usbalex/74series_game_of_life/74series_game_of_life.kicad_sch

## KiCad design 74series_game_of_life.kicad_sch (2022-06-20)

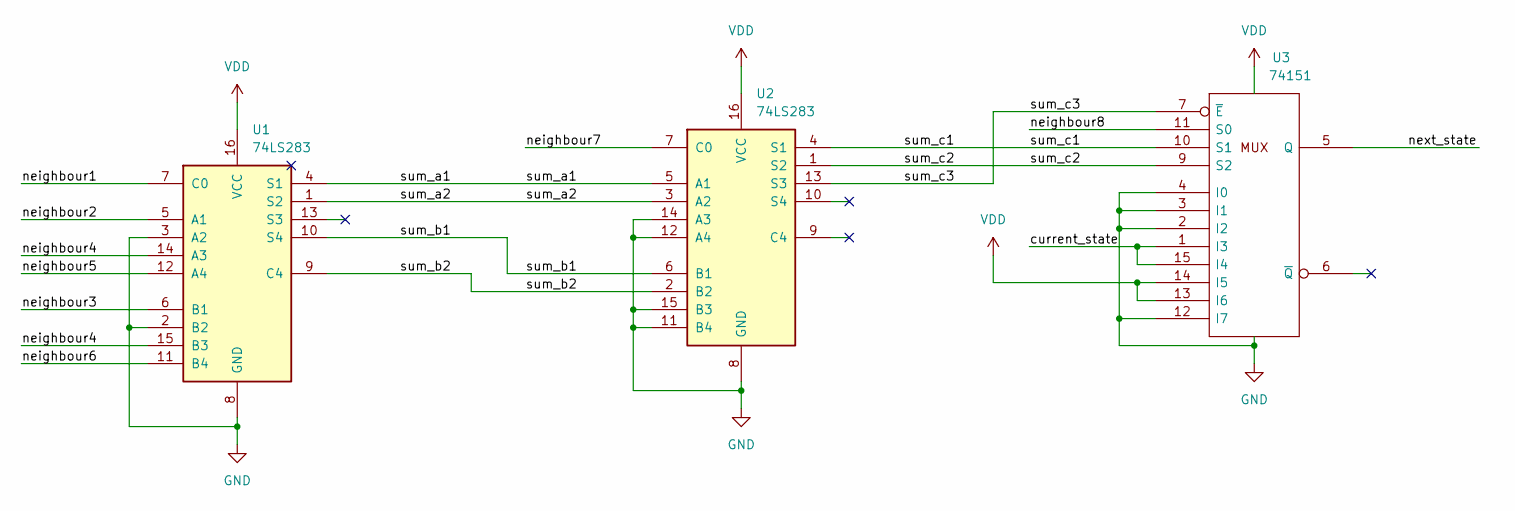
[picture p2: schematic 74series_game_of_life.kicad_sch]

Parts:
U1, U2: 74LS283
U3: 74151

Connections:
unnamed: U1.2 (B2), U1.3 (A2), U1.8 (GND)
unnamed: U2.8 (GND), U2.11 (B4), U2.12 (A4), U2.14 (A3), U2.15 (B3)
unnamed: U3.2 (I2), U3.3 (I1), U3.4 (I0), U3.8 (GND), U3.12 (I7)
unnamed: U3.13 (I6), U3.14 (I5)
current_state: U3.1 (I3), U3.15 (I4)
neighbour1: U1.7 (C0)
neighbour2: U1.5 (A1)
neighbour3: U1.6 (B1)
neighbour4: U1.14 (A3), U1.15 (B3)
neighbour5: U1.12 (A4)
neighbour6: U1.11 (B4)
neighbour7: U2.7 (C0)
neighbour8: U3.11 (S0)
next_state: U3.5 (Q)
sum_a1: U1.4 (S1), U2.5 (A1)
sum_a2: U1.1 (S2), U2.3 (A2)
sum_b1: U1.10 (S4), U2.6 (B1)
sum_b2: U1.9 (C4), U2.2 (B2)
sum_c1: U2.4 (S1), U3.10 (S1)
sum_c2: U2.1 (S2), U3.9 (S2)
sum_c3: U2.13 (S3), U3.7 (~E)
